Mehakpreet15/Mechatronics_PaperCraftMechanism/Progress images/progress.jpg

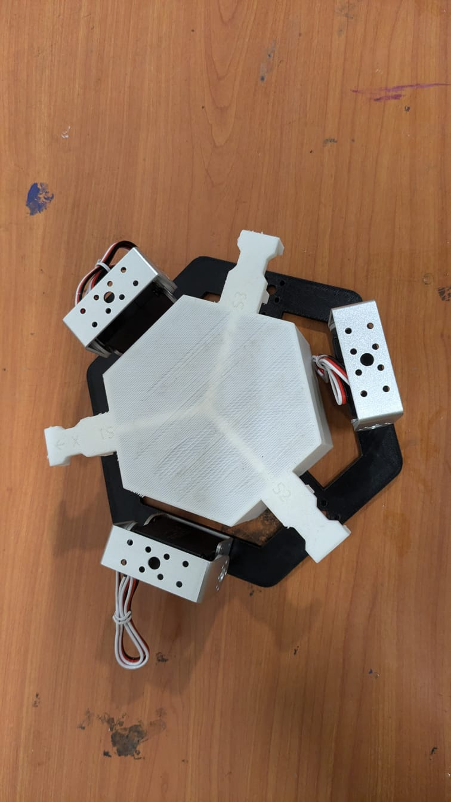
Progress images/progress.jpg
