Mehakpreet15/Mechatronics_PaperCraftMechanism/Progress images/Prototype Image.jpeg

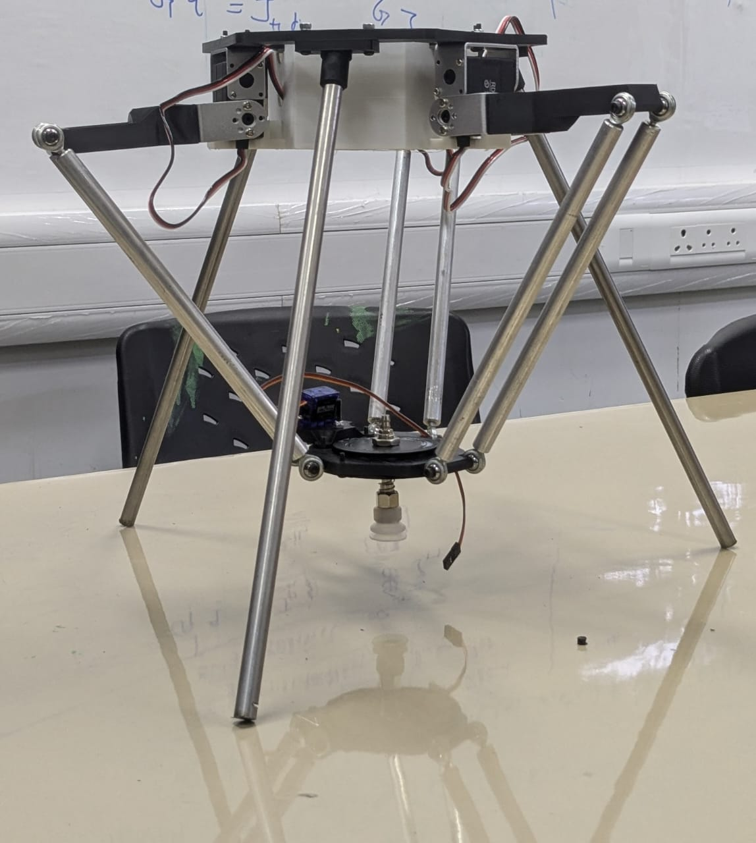
Progress images/Prototype Image.jpeg
