Mehakpreet15/Mechatronics_PaperCraftMechanism/Progress images/Screenshot 2024-09-04 183707.png

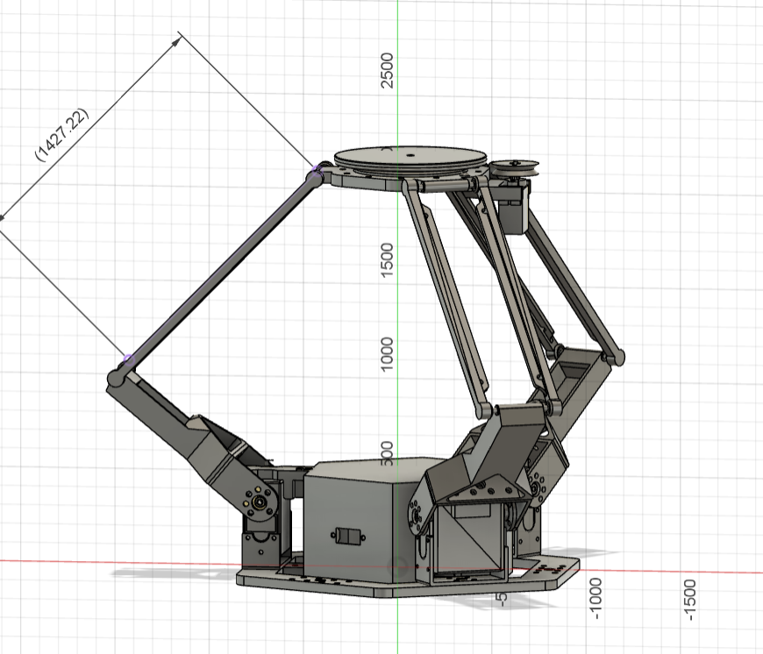
Progress images/Screenshot 2024-09-04 183707.png
